mrieker/pdp8v/maindec/docs/d0ab.tif

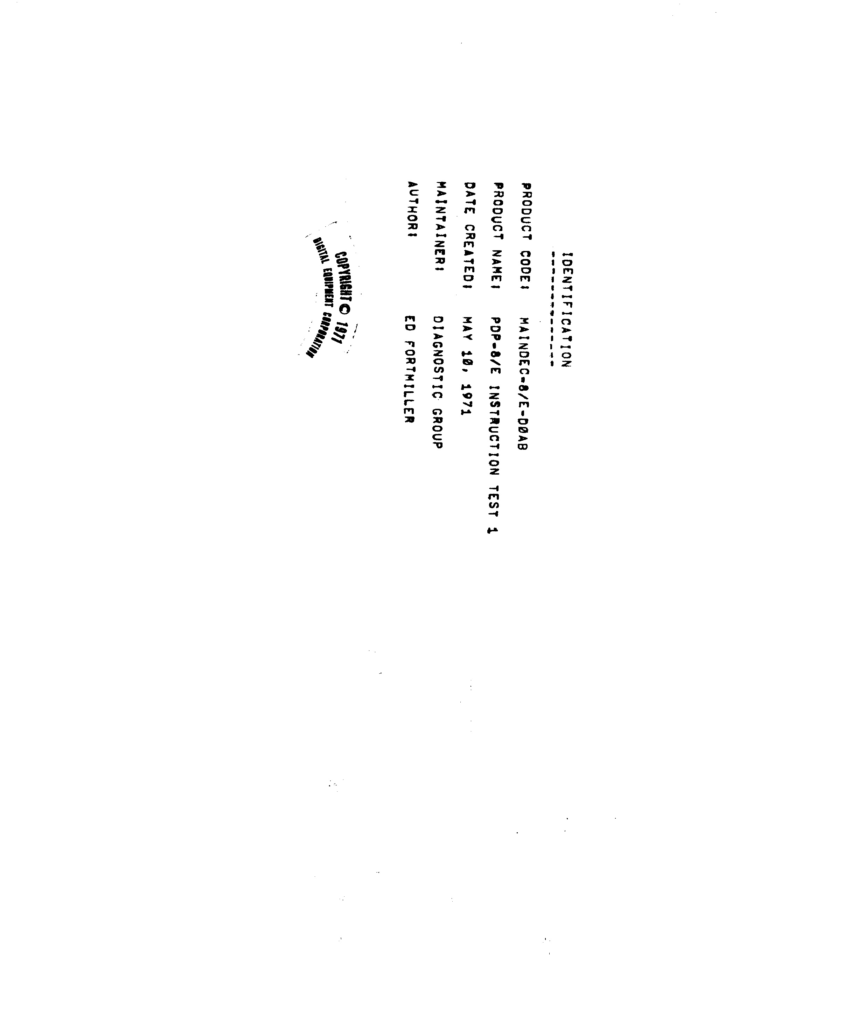
maindec/docs/d0ab.tif
