mrieker/pdp8v/maindec/docs/d0db-d.tif

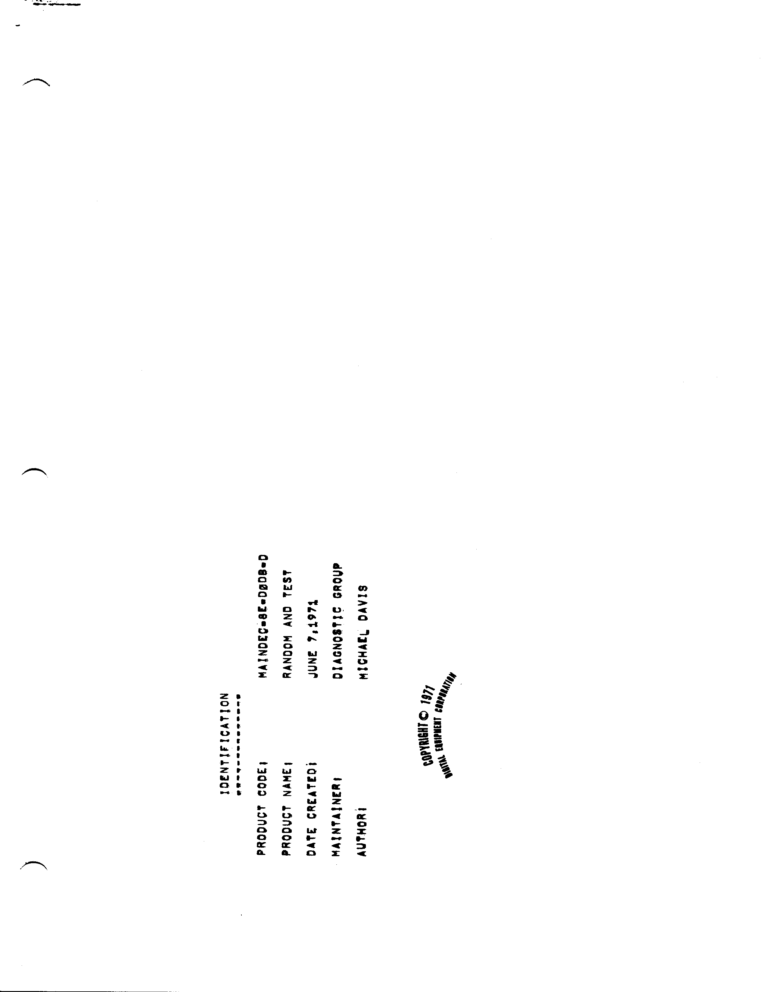
maindec/docs/d0db-d.tif
