mrieker/pdp8v/kicads/eight/single-ltspice.asc

C1: cap; 0.1µ
C2: cap; 0.1µ
C3: cap; 0.1µ
D1: zener; 3.0V
R1: res; 26.7K
R2: res; 26.7K
R3: res; 46.4K
R4: res; 150K
R5: res; 220
U1: triode; 1/2-6J6
V1: voltage; 120
V2: voltage; 96
V3: voltage; 5
Named nets: 0, OUTPUT, INPUT
1: > 4V
0: < 0V
1: > 3V
0: < 0.5V
