mrieker/pdp8v/driver/pidp.cc

//    Copyright (C) Mike Rieker, Beverly, MA USA
//    www.outerworldapps.com
//
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
//    EXPECT it to FAIL when someone's HeALTh or PROpeRTy is at RISk.
//
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
//    http://www.gnu.org/licenses/gpl-2.0.html

// operate pidp panel via gpio connector
// assumes raspberry pi gpio connector is plugged into pidp panel

#include <arpa/inet.h>
#include <errno.h>
#include <fcntl.h>
#include <netdb.h>
#include <poll.h>
#include <pthread.h>
#include <stdlib.h>
#include <string.h>
#include <time.h>
#include <unistd.h>

#include "controls.h"
#include "extarith.h"
#include "gpiolib.h"
#include "memext.h"
#include "memory.h"
#include "pidp.h"
#include "rdcyc.h"
#include "shadow.h"

// gpio pins

                    //  LR1 LR2 LR3 LR4 LR5 LR6 LR7 LR8 SR1 SR2 SR3
#define COL1    14  //  pc1 ma1 mb1 ac1 mq1 and cad df1 sw1 df1 start   [MSB]
#define COL2    15  //  pc2 ma2 mb2 ac2 mq2 tad brk df2 sw2 df2 ldaddr
#define COL3     4  //  pc3 ma3 mb3 ac3 mq3 isz ion df3 sw3 df3 dep
#define COL4     5  //   .   .   .   .   .  dca pau if1  .  if1 exam
#define COL5     6  //   .   .   .   .   .  jms run if2  .  if2 cont
#define COL6     7  //   .   .   .   .   .  jmp sc1 if3  .  if3 stop
#define COL7     8  //   .   .   .   .   .  iot sc2 lnk  .      sstep
#define COL8     9  //   .   .   .   .   .  opr sc3      .      sinst
#define COL9    10  //   .   .   .   .   .  fet sc4      .
#define COL10   11  //   .   .   .   .   .  exe sc5      .
#define COL11   12  //   .   .   .   .   .  def          .
#define COL12   13  //   .   .   .   .   .  wct          .              [LSB]

#define COLMIN 4
#define COLMASK 0xFFF0

static bool inlimbo;
static bool lastdepos;
static bool running;
static pthread_t threadid;
static uint16_t dfifswitches;
static uint16_t ledscrams[4096];
static uint16_t swunscrams[65536>>COLMIN];

static void *pidpthread (void *dummy);
static void startbutton (uint32_t buttons);
static void ldaddrbutton ();
static void deposbutton ();
static void exambutton ();
static void contbutton (uint32_t buttons);
static void stopbutton ();
static void loadpcma (uint16_t newpc, uint16_t newma);
static bool atendofmajorstate ();

void pidp_start ()
{
    ASSERT (threadid == 0);
    running = true;
    int rc = createthread (&threadid, pidpthread, NULL);
    if (rc != 0) ABORT ();
}

void pidp_stop ()
{
    running = false;
    if (threadid != 0) {
        pthread_join (threadid, NULL);
        threadid = 0;
    }
}

static void *pidpthread (void *dummy)
{
    uint32_t buttonring[8];
    uint32_t lastbuttons = 0;
    uint32_t opcodeleds[8];
    uint32_t stateleds[16];
    int buttonindex = 0;

    memset (buttonring, 0, sizeof buttonring);
    memset (opcodeleds, 0, sizeof opcodeleds);
    memset (stateleds, 0, sizeof stateleds);

    opcodeleds[0] = 1 << COL1;
    opcodeleds[1] = 1 << COL2;
    opcodeleds[2] = 1 << COL3;
    opcodeleds[3] = 1 << COL4;
    opcodeleds[4] = 1 << COL5;
    opcodeleds[5] = 1 << COL6;
    opcodeleds[6] = 1 << COL7;
    opcodeleds[7] = 1 << COL8;

    stateleds[(int)Shadow::State::FETCH1] = 1 << COL9;
    stateleds[(int)Shadow::State::FETCH2] = 1 << COL9;
    stateleds[(int)Shadow::State::DEFER1] = 1 << COL11;
    stateleds[(int)Shadow::State::DEFER2] = 1 << COL11;
    stateleds[(int)Shadow::State::DEFER3] = 1 << COL11;
    stateleds[(int)Shadow::State::EXEC1]  = 1 << COL10;
    stateleds[(int)Shadow::State::EXEC2]  = 1 << COL10;
    stateleds[(int)Shadow::State::EXEC3]  = 1 << COL10;

    for (uint16_t data = 0; data <= 07777; data ++) {
        uint16_t gpio = 0;
        if (data & 04000) gpio |= 1 << COL1;
        if (data & 02000) gpio |= 1 << COL2;
        if (data & 01000) gpio |= 1 << COL3;
        if (data & 00400) gpio |= 1 << COL4;
        if (data & 00200) gpio |= 1 << COL5;
        if (data & 00100) gpio |= 1 << COL6;
        if (data & 00040) gpio |= 1 << COL7;
        if (data & 00020) gpio |= 1 << COL8;
        if (data & 00010) gpio |= 1 << COL9;
        if (data & 00004) gpio |= 1 << COL10;
        if (data & 00002) gpio |= 1 << COL11;
        if (data & 00001) gpio |= 1 << COL12;
        ledscrams[data] = gpio;
    }

    for (uint32_t gpio = 0; gpio <= 0xFFFFU; gpio += 1 << COLMIN) {
        uint16_t data = 0;
        if (gpio & (1 << COL1))  data |= 04000;
        if (gpio & (1 << COL2))  data |= 02000;
        if (gpio & (1 << COL3))  data |= 01000;
        if (gpio & (1 << COL4))  data |= 00400;
        if (gpio & (1 << COL5))  data |= 00200;
        if (gpio & (1 << COL6))  data |= 00100;
        if (gpio & (1 << COL7))  data |= 00040;
        if (gpio & (1 << COL8))  data |= 00020;
        if (gpio & (1 << COL9))  data |= 00010;
        if (gpio & (1 << COL10)) data |= 00004;
        if (gpio & (1 << COL11)) data |= 00002;
        if (gpio & (1 << COL12)) data |= 00001;
        swunscrams[gpio>>COLMIN] = data;
    }

    // set up sequence number gt anything previously used
    PiDPMsg pidpmsg;
    memset (&pidpmsg, 0, sizeof pidpmsg);
    struct timespec nowts;
    if (clock_gettime (CLOCK_REALTIME, &nowts) < 0) ABORT ();
    pidpmsg.seq = nowts.tv_sec * 1000000000ULL + nowts.tv_nsec;

    while (running) {
        pidpmsg.seq ++;

        uint32_t lr7 =
            (memext.intenabd ()  ? (1 << COL3) : 0) |               // ION
            (waitingforinterrupt ? (1 << COL4) : 0) |               // PAUSE (we use it for 'wait for interrupt')
            (ctl_isstopped ()    ? 0 : (1 << COL5)) |               // RUN
            ledscrams[extarith.stepcount<<2];                       // SC

        uint16_t membuffer;
        uint32_t lr6 = 0;
        if (inlimbo) {

            // ldaddr/exam/depos, show mem contents
            membuffer = memarray[memext.iframe|shadow.r.ma];
        } else {

            // not doing ldaddr/exam/depos, show processor state
            Shadow::State st = (Shadow::State) (shadow.r.state & 15);
            lr6 = stateleds[(int)st];
            if ((st != Shadow::State::FETCH1) && (st != Shadow::State::INTAK1)) {
                uint32_t ir = (st == Shadow::State::FETCH2) ? (gpio->readgpio () & G_DATA) / G_DATA0 : shadow.r.ir;
                lr6 |= opcodeleds[(ir>>9)&7];
            }

            if (st == Shadow::State::INTAK1) lr7 |= 1 << COL2;      // BREAK (we use it for INTAK1 cycle)

            membuffer = (gpio->readgpio () & G_DATA) / G_DATA0;     // show what is on gpio bus
        }

        uint32_t lr8 =
            ledscrams[(memext.dframe>>3)|(memext.iframe>>6)] |
            (shadow.r.link ? (1 << COL7) : 0);

        // output LED rows
        pidpmsg.ledrows[0] = ledscrams[shadow.r.pc];
        pidpmsg.ledrows[1] = ledscrams[shadow.r.ma];
        pidpmsg.ledrows[2] = ledscrams[membuffer];
        pidpmsg.ledrows[3] = ledscrams[shadow.r.ac];
        pidpmsg.ledrows[4] = ledscrams[extarith.multquot];
        pidpmsg.ledrows[5] = lr6;
        pidpmsg.ledrows[6] = lr7;
        pidpmsg.ledrows[7] = lr8;

        // ... also read switches
        if (! pidp_proc (&pidpmsg)) continue;

        // row 1 - switch register switches
        switchregister = swunscrams[(~pidpmsg.swrows[0]&COLMASK)>>COLMIN];

        // row 2 - data field, instr field switches
        dfifswitches   = swunscrams[(~pidpmsg.swrows[1]&COLMASK)>>COLMIN];

        // row 3 - control buttons
        uint32_t buttons = ~ pidpmsg.swrows[2] & COLMASK;
        buttonring[buttonindex] = buttons;
        buttonindex = (buttonindex + 1) % 8;

        // if button went from not pressed to pressed, perform function
        uint32_t butpressed = ~ lastbuttons & buttons;

        // if buttons have been steady past 8 iterations, we consider the buttons valid
        for (int i = 0; ++ i < 8;) {
            if (buttonring[i] != buttons) goto badbuttons;
        }

        if (butpressed & (1 << COL1)) startbutton (buttons);
        if (butpressed & (1 << COL2)) ldaddrbutton ();
        if (butpressed & (1 << COL3)) deposbutton ();
        if (butpressed & (1 << COL4)) exambutton ();
        if (butpressed & (1 << COL5)) contbutton (buttons);
        if (butpressed & (1 << COL6)) stopbutton ();
        lastbuttons = buttons;
    badbuttons:;
    }

    return NULL;
}

// reset I/O then start at address in IF/PC
static void startbutton (uint32_t buttons)
{
    if (ctl_isstopped ()) {
        ctl_reset (memext.iframe | shadow.r.pc, true);
        contbutton (buttons);
    }
}

// load switch register into MA and PC, then show contents of that location
static void ldaddrbutton ()
{
    if (ctl_isstopped ()) {
        loadpcma (switchregister, switchregister);
        memext.dframe = (dfifswitches & 07000) << 3;
        memext.iframe = (dfifswitches & 00700) << 6;
        inlimbo   = true;
        lastdepos = false;
    }
}

// if last button was deposit, increment MA
// then in any case, deposit switch register into MA location
static void deposbutton ()
{
    if (ctl_isstopped ()) {
        uint16_t ma = shadow.r.ma;
        if (lastdepos) {
            ma = (ma + 1) & 07777;
            loadpcma (shadow.r.pc, ma);
        }
        memarray[memext.iframe|ma] = switchregister;
        inlimbo   = true;
        lastdepos = true;
    }
}

// if last button wasn't deposit, increment MA
// then in any case, show memory contents
static void exambutton ()
{
    if (ctl_isstopped ()) {
        uint16_t ma = shadow.r.ma;
        if (! lastdepos) {
            ma = (ma + 1) & 07777;
            loadpcma (shadow.r.pc, ma);
        }
        inlimbo   = true;
        lastdepos = false;
    }
}

// resume execution at program counter location, subject to step switches
static void contbutton (uint32_t buttons)
{
    if (ctl_isstopped ()) {
        if (buttons & (1 << COL7)) {
            do ctl_stepcyc ();  // single step - step one major state
            while (! atendofmajorstate ());
        } else if (buttons & (1 << COL8)) {
            ctl_stepins ();     // single instr - step one instruction
                                // stops in middle of FETCH2 or middle of INTAK1
        } else {
            ctl_run ();         // neither - continuous run
        }
        inlimbo   = false;
        lastdepos = false;
    }
}

// stop executing instructions
static void stopbutton ()
{
    if (! ctl_isstopped ()) {
        ctl_stop ();            // stops in middle of any cycle
        while (! atendofmajorstate ()) {
            ctl_stepcyc ();     // cycle to end of major state
        }
        inlimbo   = false;
        lastdepos = false;
    }
}

// load tubes' program counter and memory address register with given values
// returns with tubes in middle of FETCH2 with clock still high
static void loadpcma (uint16_t newpc, uint16_t newma)
{
    uint16_t saveac = shadow.r.ac;
    bool savelink = shadow.r.link;
    if (! ctl_ldregs (savelink, saveac, newma, newpc)) ABORT ();
}

// stopped in middle of some cycle - see if it is the last cycle of a major state
static bool atendofmajorstate ()
{
    Shadow::State st = shadow.r.state;
    switch (st) {
        case Shadow::State::FETCH1: return false;
        case Shadow::State::FETCH2: return true;
        case Shadow::State::DEFER1: return false;
        case Shadow::State::DEFER2: return (shadow.r.ma & 07770) != 00010;
        case Shadow::State::DEFER3: return true;
        case Shadow::State::ARITH1: return false;
        case Shadow::State::AND2  : return true;
        case Shadow::State::TAD2  : return false;
        case Shadow::State::TAD3  : return true;
        case Shadow::State::ISZ1  : return false;
        case Shadow::State::ISZ2  : return false;
        case Shadow::State::ISZ3  : return true;
        case Shadow::State::DCA1  : return false;
        case Shadow::State::DCA2  : return true;
        case Shadow::State::JMP1  : return true;
        case Shadow::State::JMS1  : return false;
        case Shadow::State::JMS2  : return false;
        case Shadow::State::JMS3  : return true;
        case Shadow::State::IOT1  : return false;
        case Shadow::State::IOT2  : return true;
        case Shadow::State::GRPA1 : return true;
        case Shadow::State::GRPB1 : return true;
        case Shadow::State::INTAK1: return true;
        default: ABORT ();
    }
}
