mrieker/pdp8v/zynq/ledpins.xdc

set_property PACKAGE_PIN Y16 [get_ports LEDoutG_0]
set_property PACKAGE_PIN Y17 [get_ports LEDoutB_0]
set_property PACKAGE_PIN R14 [get_ports LEDoutR_0]
set_property IOSTANDARD LVCMOS33 [get_ports LEDoutB_0]
set_property IOSTANDARD LVCMOS33 [get_ports LEDoutG_0]
set_property IOSTANDARD LVCMOS33 [get_ports LEDoutR_0]

set_property PACKAGE_PIN G15 [get_ports EXTSDA_0]   ;# CN2-69
set_property PACKAGE_PIN H20 [get_ports EXTSCL_0]   ;# CN2-65
set_property IOSTANDARD LVCMOS33 [get_ports EXTSDA_0]
set_property IOSTANDARD LVCMOS33 [get_ports EXTSCL_0]
