mrieker/pdp8v/driver/GUIRasPiCtl.cc

//    Copyright (C) Mike Rieker, Beverly, MA USA
//    www.outerworldapps.com
//
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
//    EXPECT it to FAIL when someone's HeALTh or PROpeRTy is at RISk.
//
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
//    http://www.gnu.org/licenses/gpl-2.0.html

// inteface GUI java program to raspictl

#include "GUIRasPiCtl.h"

#include <alloca.h>
#include <pthread.h>
#include <string.h>

#include "controls.h"
#include "disassemble.h"
#include "gpiolib.h"
#include "iodevs.h"
#include "memext.h"
#include "memory.h"
#include "miscdefs.h"
#include "shadow.h"

#define EXCKR(x) x; if (env->ExceptionCheck ()) return 0

extern GpioLib *gpio;

int main (int argc, char **argv);

JNIEXPORT jint JNICALL Java_GUIRasPiCtl_main (JNIEnv *env, jclass klass, jobjectArray args)
{
    // see how many strings passed in args
    int argc = EXCKR (env->GetArrayLength (args));

    // allocate an array of pointers (one extra for NULL terminator)
    char **argv = (char **) alloca ((argc + 1) * sizeof *argv);

    // copy strings into array
    for (int i = 0; i < argc; i ++) {

        // get string from arg array element
        jstring argstr = (jstring) EXCKR (env->GetObjectArrayElement (args, i));

        // convert to UTF-8 byte array
        char const *argutf = EXCKR (env->GetStringUTFChars (argstr, NULL));

        // copy to stack
        int arglen = strlen (argutf);
        char *arg = (char *) alloca (arglen + 1);
        memcpy (arg, argutf, arglen);
        arg[arglen] = 0;
        argv[i] = arg;

        // release java string
        env->ReleaseStringUTFChars (argstr, argutf);
    }

    // NULL terminate argument list and call main
    argv[argc] = NULL;
    return main (argc, argv);
}

JNIEXPORT jint JNICALL Java_GUIRasPiCtl_getacl (JNIEnv *env, jclass klass)
{
    return (shadow.r.link ? 010000 : 0) | shadow.r.ac;
}

JNIEXPORT jint JNICALL Java_GUIRasPiCtl_getma (JNIEnv *env, jclass klass)
{
    return shadow.r.ma | memext.dframe;
}

JNIEXPORT jint JNICALL Java_GUIRasPiCtl_getpc (JNIEnv *env, jclass klass)
{
    return shadow.r.pc | memext.iframe;
}

JNIEXPORT jint JNICALL Java_GUIRasPiCtl_getir (JNIEnv *env, jclass klass)
{
    return shadow.r.ir;
}

JNIEXPORT jint JNICALL Java_GUIRasPiCtl_getst (JNIEnv *env, jclass klass)
{
    return (jint) shadow.r.state;
}

JNIEXPORT jint JNICALL Java_GUIRasPiCtl_getgpio (JNIEnv *env, jclass klass)
{
    GpioLib *g = gpio;
    if (g == NULL) return -1;
    return g->readgpio ();
}

JNIEXPORT jlong JNICALL Java_GUIRasPiCtl_getcycs (JNIEnv *env, jclass klass)
{
    return shadow.getcycles ();
}

JNIEXPORT jint JNICALL Java_GUIRasPiCtl_getsr (JNIEnv *env, jclass klass)
{
    return switchregister;
}

JNIEXPORT void JNICALL Java_GUIRasPiCtl_setsr (JNIEnv *env, jclass klass, jint sr)
{
    switchregister = sr & 32767;
}

// returns true = processor is stopped
//        false = processor is running
JNIEXPORT jboolean JNICALL Java_GUIRasPiCtl_getstop (JNIEnv *env, jclass klass)
{
    return ctl_isstopped ();
}

// input:
//  stop = true: stop the processor
//        false: run the processor
// returns:
//    true = was stopped
//   false = was running
JNIEXPORT jboolean JNICALL Java_GUIRasPiCtl_setstop (JNIEnv *env, jclass klass, jboolean stop)
{
    return stop ? ctl_stop () : ctl_run ();
}

// returns:
//   true = was stopped, stepped one cycle, now stopped again
//  false = was running, not stepped, still running
JNIEXPORT jboolean JNICALL Java_GUIRasPiCtl_stepcyc (JNIEnv *env, jclass klass)
{
    return ctl_stepcyc ();
}

// returns:
//   true = was stopped, stepped to FETCH2 or INTAK1, now stopped again
//  false = was running, not stepped, still running
JNIEXPORT jboolean JNICALL Java_GUIRasPiCtl_stepins (JNIEnv *env, jclass klass)
{
    return ctl_stepins ();
}

JNIEXPORT jstring JNICALL Java_GUIRasPiCtl_disassemble (JNIEnv *env, jclass klass, jint ir, jint pc)
{
    char const *io = iodisas (ir);
    if (io != NULL) return env->NewStringUTF (io);
    std::string str = disassemble (ir, pc);
    return env->NewStringUTF (str.c_str ());
}

JNIEXPORT jint JNICALL Java_GUIRasPiCtl_rdmem (JNIEnv *env, jclass klass, jint addr)
{
    if (addr >= MEMSIZE) return -1;
    return memarray[addr];
}

JNIEXPORT jint JNICALL Java_GUIRasPiCtl_wrmem (JNIEnv *env, jclass klass, jint addr, jint data)
{
    if (addr >= MEMSIZE) return -1;
    data &= 07777;
    memarray[addr] = data;
    return data;
}

// returns:
//   true = was stopped, reset, now stopped again at end of FETCH1
//  false = failed
JNIEXPORT jboolean JNICALL Java_GUIRasPiCtl_reset (JNIEnv *env, jclass klass, jint addr, jboolean resio)
{
    return ctl_reset (addr, resio);
}

// load registers
// returns:
//   true = was stopped, reset, now stopped again at end of FETCH1
//  false = failed
JNIEXPORT jboolean JNICALL Java_GUIRasPiCtl_ldregs (JNIEnv *env, jclass klass, jboolean link, jint ac, jint ma, jint pc)
{
    return ctl_ldregs (link, ac, ma, pc);
}
