mrieker/pdp8v/driver/exptimingioin.cc

// runs on raspi plugged into experiment board (exp)
// measures clock frequency of IOS,MQL->IOIN gate

// ./loadmod.sh
// ./exptimingioin.armv6l

#include <stdio.h>
#include <string.h>
#include <time.h>
#include <unistd.h>

#include "gpiolib.h"
#include "rdcyc.h"

static GpioLib *gpiolib;
static uint32_t fullus;

static void waitfull ();

int main ()
{
    struct timespec finished, started;

    setlinebuf (stdout);

    gpiolib = new PhysLib (10, true);
    gpiolib->open ();
    gpiolib->writegpio (false, G_RESET);
    gpiolib->halfcycle ();
    gpiolib->halfcycle ();
    gpiolib->halfcycle ();
    gpiolib->writegpio (false, 0);

    for (fullus = 1; fullus <= 20; fullus ++) {
        int bad = 0;
        if (clock_gettime (CLOCK_REALTIME, &started) < 0) ABORT ();
        for (int i = 0; i < 10000; i ++) {
            uint32_t gray = (i & 3) ^ ((i & 3) >> 1);
            uint32_t sent = ((gray & 1) ? G_LINK : 0) | ((gray & 2) ? G_IOS : 0);
            gpiolib->writegpio (true, sent);
            waitfull ();
            uint32_t rcvd = gpiolib->readgpio () & G_IOIN;
            bad += (((sent / G_LINK) ^ (sent / G_IOS)) & 1) ^ (rcvd / G_IOIN);
        }
        if (clock_gettime (CLOCK_REALTIME, &finished) < 0) ABORT ();
        uint64_t elapsedns = (uint64_t) (finished.tv_sec - started.tv_sec) * 1000000000 + finished.tv_nsec - started.tv_nsec;
        printf (" fullus = %2u  bad = %5u/10000  %6llu Hz\n", fullus, bad, 10000000000000ULL / elapsedns);
    }
    return 0;
}

static void waitfull ()
{
    uint32_t start = rdcyc ();
    while (rdcyc () - start < fullus) { }
}
