mrieker/pdp8v/driver/iodevtc08.cc

//    Copyright (C) Mike Rieker, Beverly, MA USA
//    www.outerworldapps.com
//
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
//    EXPECT it to FAIL when someone's HeALTh or PROpeRTy is at RISk.
//
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
//    http://www.gnu.org/licenses/gpl-2.0.html

// TC08 controller maintenance 1970
// boot code: OS/8 Handbook April 1974, p41
//  07613: 06774, 01222, 06766, 06771, 05216, 01223, 05215, 00600, 00220

// files are 1474*129*2 bytes = 380292 bytes
// loading a file read/write extends/truncates it to correct size
// if read/write file was null length, it is formatted for OS/8

#include <errno.h>
#include <fcntl.h>
#include <signal.h>
#include <stdarg.h>
#include <stdio.h>
#include <string.h>
#include <sys/file.h>
#include <sys/mman.h>
#include <sys/time.h>
#include <unistd.h>

#include "dyndis.h"
#include "gpiolib.h"
#include "iodevtc08.h"
#include "memext.h"
#include "memory.h"
#include "rdcyc.h"
#include "shadow.h"

/*
  status_a:
    | unitsel   |REV|GO |CON|  opcode   |IEN|PAF|PSF|
    +---+---+---+---+---+---+---+---+---+---+---+---+
    | 4   2   1 | 4   2   1 | 4   2   1 | 4   2   1 |

  status_b:
    |ERR|   |EOT|SEL|       | dma field |       |SUC|
    +---+---+---+---+---+---+---+---+---+---+---+---+
    | 4   2   1 | 4   2   1 | 4   2   1 | 4   2   1 |
*/

#define DBGPR if (shm->debug > 0) dbgpr

#define MIN(a,b) (((a) < (b)) ? (a) : (b))

#define BLOCKSPERTAPE 1474  // 02702
#define WORDSPERBLOCK 129
#define BYTESPERBLOCK (WORDSPERBLOCK*2)
#define UNLOADNS 5000000000ULL

#define CONTIN (shm->status_a & 00100)
#define NORMAL (! CONTIN)

#define REVBIT 00400
#define GOBIT  00200

#define REVERS (shm->status_a & REVBIT)
#define FORWRD (! REVERS)

#define DTFLAG 00001    // successful completion
#define ERFLAG 04000    // error completion
#define ERRORS 07700
#define ENDTAP 05000
#define SELERR 04400

#define INTENA 00004    // interrupt enable
#define INTREQ 04001    // request interrupt if error or success

#define IDWC 07754      // memory word containing 2s comp dma word count
#define IDCA 07755      // memory word containing dma address minus one

IODevTC08 iodevtc08;

static uint16_t ocarray[4096];

static IODevOps const iodevops[] = {
    { 06761, "DTRA (TC08) read status register A" },
    { 06762, "DTCA (TC08) clear status register A" },
    { 06764, "DTXA (TC08) load status register A" },
    { 06766, "DTLA (TC08) clear and load status register A" },
    { 06771, "DTSF (TC08) skip on flag" },
    { 06772, "DTRB (TC08) read status register B" },
    { 06773, "DTSF DTRB (TC08) skip on flag, read status register B" },
    { 06774, "DTXB (TC08) load status register B and clear accumulator" },
};

static char const *const cmdmnes[8] = { "MOVE", "SRCH", "RDAT", "RALL", "WDAT", "WALL", "WTIM", "ERR7" };

static uint64_t getnowns ();
static bool dmareadoverwritesinstructions (uint16_t field, uint16_t idca, uint16_t idwc);
static SCRetErr *writeformat (int fd);

IODevTC08::IODevTC08 ()
{
    opscount = sizeof iodevops / sizeof iodevops[0];
    opsarray = iodevops;

    iodevname = "tc08";

    // initialize obverse complement lookup table
    //   abcdefghijkl <=> ~jklghidefabc
    for (int i = 0; i < 4096; i ++) {
        uint16_t reverse = 07777;
        for (int j = 0; j < 12; j += 3) {
            uint32_t threebits = (i >> j) & 7;
            reverse -= threebits << (9 - j);
        }
        ocarray[i] = reverse;
    }

    // initialize everything
    this->shm = NULL;
    this->shmfd = -1;
    this->allowskipopt = true;
    this->dskpwait = false;
}

IODevTC08::~IODevTC08 ()
{
    // nothing to do if shared memory was never set up
    if (this->shm == NULL) return;

    // lock and unlock for a barrier
    pthread_mutex_lock (&shm->lock);
    shm->exiting = true;
    pthread_mutex_unlock (&shm->lock);

    // stop thread
    this->ioreset ();

    // delete shared memory
    shm_unlink (shmname);
    for (int i = 0; i < 8; i ++) {
        close (shm->drives[i].dtfd);
        shm->drives[i].dtfd = -1;
        shm->drives[i].fname[0] = 0;
    }
    munmap (this->shm, sizeof *this->shm);
    this->shm = NULL;
    close (this->shmfd);
    this->shmfd = -1;
}

// reset the device
// - kill thread
void IODevTC08::ioreset ()
{
    // nothing to do if shared memory isn't set up
    if (this->shm == NULL) return;

    pthread_mutex_lock (&shm->lock);

    // if another thread is doing the reset, wait for it to complete
    if (shm->resetting) {
        do pthread_cond_wait (&shm->cond, &shm->lock);
        while (shm->resetting);
    } else {

        // no other thread doing reset, tell others we are doing reset
        shm->resetting = true;
        pthread_cond_broadcast (&shm->cond);

        // if our thread is running, tell it to stop and wait for it to stop
        if (shm->threadid != 0) {
            pthread_mutex_unlock (&shm->lock);
            pthread_join (shm->threadid, NULL);
            pthread_mutex_lock (&shm->lock);
            shm->threadid = 0;
        }

        // clear status to reset state
        shm->status_a = 0;
        shm->status_b = 0;
        clrintreqmask (IRQ_DTAPE);

        shm->resetting = false;
        pthread_cond_broadcast (&shm->cond);
    }

    pthread_mutex_unlock (&shm->lock);
}

// load/unload files
SCRet *IODevTC08::scriptcmd (int argc, char const *const *argv)
{
    // create shared memory if not already
    if (this->shm == NULL) {

        // create shared memory for tc08status.cc program to access tape state
        this->shmfd = shm_open (shmname, O_RDWR | O_CREAT, 0600);
        if (this->shmfd < 0) {
            fprintf (stderr, "IODevTC08::IODevTC08: error creating shared memory %s: %m\n", shmname);
            ABORT ();
        }
        if (ftruncate (this->shmfd, sizeof *this->shm) < 0) {
            fprintf (stderr, "IODevTC08::IODevTC08: error setting shared memory %s size: %m\n", shmname);
            close (this->shmfd);
            this->shmfd = -1;
            shm_unlink (shmname);
            ABORT ();
        }

        // map it to va space and zero it out
        void *shmptr = mmap (NULL, sizeof *this->shm, PROT_READ | PROT_WRITE, MAP_SHARED, this->shmfd, 0);
        if (shmptr == MAP_FAILED) {
            fprintf (stderr, "IODevTC08::IODevTC08: error accessing shared memory %s: %m\n", shmname);
            close (this->shmfd);
            this->shmfd = -1;
            shm_unlink (shmname);
            ABORT ();
        }

        IODevTC08Shm *lclshm = (IODevTC08Shm *) shmptr;
        memset (lclshm, 0, sizeof *lclshm);

        // initialize everything
        pthread_condattr_t condattrs;
        if (pthread_condattr_init (&condattrs) != 0) ABORT ();
        if (pthread_condattr_setpshared (&condattrs, PTHREAD_PROCESS_SHARED) != 0) ABORT ();
        if (pthread_cond_init (&lclshm->cond, &condattrs) != 0) ABORT ();

        pthread_mutexattr_t lockattrs;
        if (pthread_mutexattr_init (&lockattrs) != 0) ABORT ();
        if (pthread_mutexattr_setpshared (&lockattrs, PTHREAD_PROCESS_SHARED) != 0) ABORT ();
        if (pthread_mutex_init (&lclshm->lock, &lockattrs) != 0) ABORT ();

        lclshm->dtpid = getpid ();
        for (int i = 0; i < 8; i ++) {
            lclshm->drives[i].dtfd = -1;
            lclshm->drives[i].unldat = 0xFFFFFFFFFFFFFFFFULL;
        }

        // lock and unlock for a barrier
        pthread_mutex_lock (&lclshm->lock);
        lclshm->initted = true;
        pthread_mutex_unlock (&lclshm->lock);
        this->shm = lclshm;
    }

    // debug <level>
    if (strcmp (argv[0], "debug") == 0) {
        if (argc == 1) {
            return new SCRetInt (shm->debug);
        }

        if (argc == 2) {
            shm->debug = atoi (argv[1]);
            return NULL;
        }

        return new SCRetErr ("iodev %s debug <level>", iodevname);
    }

    if (strcmp (argv[0], "help") == 0) {
        puts ("");
        puts ("valid sub-commands:");
        puts ("");
        puts ("  debug                           - get debug level");
        puts ("  debug <level>                   - set debug level");
        puts ("  loaded <drivenumber>            - see what file is loaded on drive");
        puts ("                                    first char -: read-only; +: read/write");
        puts ("  loadro <drivenumber> <filename> - load file write-locked");
        puts ("  loadrw <drivenumber> <filename> - load file write-enabled");
        puts ("  unload <drivenumber>            - unload file - drive reports offline");
        puts ("");
        return NULL;
    }

    // return name of file loaded on drive (null if none)
    if (strcmp (argv[0], "loaded") == 0) {
        if (argc == 2) {
            char *p;
            int driveno = strtol (argv[1], &p, 0);
            if ((*p != 0) || (driveno < 0) || (driveno > 7)) return new SCRetErr ("drivenumber %s not in range 0..7", argv[1]);
            IODevTC08Drive *drive = &shm->drives[driveno];
            if (drive->dtfd < 0) return NULL;
            return new SCRetStr ("%c%s", drive->rdonly ? '-' : '+', drive->fname);
        }

        return new SCRetErr ("iodev tc08 loaded <drivenumber>");
    }

    // loadro/loadrw <drivenumber> <filename>
    bool loadro = (strcmp (argv[0], "loadro") == 0);
    bool loadrw = (strcmp (argv[0], "loadrw") == 0);
    if (loadro | loadrw) {
        if (argc == 3) {
            char *p;
            int driveno = strtol (argv[1], &p, 0);
            if ((*p != 0) || (driveno < 0) || (driveno > 7)) return new SCRetErr ("drivenumber %s not in range 0..7", argv[1]);
            int fd = open (argv[2], loadrw ? O_RDWR | O_CREAT : O_RDONLY, 0666);
            if (fd < 0) return new SCRetErr (strerror (errno));
            char *lockerr = lockfile (fd, loadro ? F_RDLCK : F_WRLCK);
            if (lockerr != NULL) {
                SCRetErr *err = new SCRetErr ("%s", lockerr);
                close (fd);
                free (lockerr);
                return err;
            }
            long oldsize = lseek (fd, 0, SEEK_END);
            if (loadrw && (ftruncate (fd, BYTESPERBLOCK * BLOCKSPERTAPE) < 0)) {
                SCRetErr *err = new SCRetErr ("%m");
                close (fd);
                return err;
            }
            if (loadrw && (oldsize == 0)) {
                SCRetErr *err = writeformat (fd);
                if (err != NULL) {
                    close (fd);
                    return err;
                }
            }
            fprintf (stderr, "IODevTC08::scriptcmd: drive %d loaded with read%s file %s\n", driveno, (loadro ? "-only" : "/write"), argv[2]);
            pthread_mutex_lock (&shm->lock);
            IODevTC08Drive *drive = &shm->drives[driveno];
            close (drive->dtfd);
            drive->dtfd    = fd;
            drive->rdonly  = loadro;
            drive->tapepos = 0;
            drive->unldat  = 0xFFFFFFFFFFFFFFFFULL;
            strncpy (drive->fname, argv[2], sizeof drive->fname);
            drive->fname[sizeof drive->fname-1] = 0;
            pthread_mutex_unlock (&shm->lock);
            return NULL;
        }

        return new SCRetErr ("iodev tc08 loadro/loadrw <drivenumber> <filename>");
    }

    // unload <drivenumber>
    if (strcmp (argv[0], "unload") == 0) {
        if (argc == 2) {
            char *p;
            int driveno = strtol (argv[1], &p, 0);
            if ((*p != 0) || (driveno < 0) || (driveno > 7)) return new SCRetErr ("drivenumber %s not in range 0..7", argv[1]);
            pthread_mutex_lock (&shm->lock);
            this->unloadrive (driveno);
            pthread_mutex_unlock (&shm->lock);
            return NULL;
        }

        return new SCRetErr ("iodev tc08 unload <drivenumber>");
    }

    return new SCRetErr ("unknown tape command %s - valid: help loaded loadro loadrw unload", argv[0]);
}

// perform i/o instruction
uint16_t IODevTC08::ioinstr (uint16_t opcode, uint16_t input)
{
    return (this->shm == NULL) ? ioinstroffline (opcode, input) : ioinstronline (opcode, input);
}

// - no shared memory, report drive offline status
uint16_t IODevTC08::ioinstroffline (uint16_t opcode, uint16_t input)
{
    switch (opcode) {

        // DTRA (TC08) read status register A
        // p 396
        case 06761: {
            break;
        }

        // DTCA (TC08) clear status register A
        case 06762: {
            break;
        }

        // DTLA (TC08) clear and load status register A
        case 06766: {
            // fall through
        }

        // DTXA (TC08) load status register A
        case 06764: {
            input &= IO_LINK;
            break;
        }

        // DTSF (TC08) skip on flag
        case 06771: {
            input |= IO_SKIP;
            break;
        }

        // DTRB (TC08) read status register B
        case 06772: {
            input |= SELERR;
            break;
        }

        // DTSF (TC08) skip on flag
        // DTRB (TC08) read status register B
        case 06773: {
            input |= IO_SKIP | SELERR;
            break;
        }

        // DTXB (TC08) load status register B <05:03> and clear accumulator
        case 06774: {
            input &= IO_LINK;
            break;
        }

        default: {
            input = UNSUPIO;
            break;
        }
    }
    return input;
}

// - have shared memory, process i/o instruction
uint16_t IODevTC08::ioinstronline (uint16_t opcode, uint16_t input)
{
    pthread_mutex_lock (&shm->lock);

    uint16_t oldstata = shm->status_a;

    DBGPR (2, "IODevTC08::ioinstr: %05o %s\n", lastreadaddr, iodisas (opcode));

    switch (opcode) {

        // DTRA (TC08) read status register A
        // p 396
        case 06761: {
            DBGPR (2, "IODevTC08::ioinstr: read status_a %04o\n", shm->status_a);
            input |= shm->status_a;
            break;
        }

        // DTCA (TC08) clear status register A
        case 06762: {
            DBGPR (2, "IODevTC08::ioinstr: clear status_a\n");
            shm->status_a = 0;
            updateirq ();
            break;
        }

        // DTLA (TC08) clear and load status register A
        case 06766: {
            DBGPR (2, "IODevTC08::ioinstr: clear status_a\n");
            shm->status_a = 0;
            // fall through
        }

        // DTXA (TC08) load status register A
        case 06764: {
            shm->status_a ^= input & 07774;
            DBGPR (2, "IODevTC08::ioinstr: xor status_a with %04o giving %04o\n", input & 07774, shm->status_a);
            if (! (input & 00001)) {
                DBGPR (2, "IODevTC08::ioinstr: clear dectape flag\n");
                shm->status_b &= ~ DTFLAG;  // clear dectape flag
            }
            if (! (input & 00002)) {
                DBGPR (2, "IODevTC08::ioinstr: clear error flags\n");
                shm->status_b &= ~ ERRORS;  // clear all error flags
            }
            updateirq ();

            int driveno = (shm->status_a >> 9) & 7;
            IODevTC08Drive *drive = &shm->drives[driveno];
            drive->unldat = 0xFFFFFFFFFFFFFFFFULL;
            DBGPR (1, "IODevTC08::ioinstr: st_A=%04o  st_B=%04o  startio  %o %s %s %s %s  tpos=%04o%c\n",
                    shm->status_a, shm->status_b, (shm->status_a >> 9) & 7, CONTIN ? "CON" : "NOR",
                    (shm->status_a & REVBIT) ? "REV" : "FWD", (shm->status_a & GOBIT) ? "GO" : "ST",
                    cmdmnes[(shm->status_a&070)>>3], drive->tapepos / 4, (drive->tapepos & 3) + 'a');

            if ((shm->status_a ^ oldstata) & (GOBIT | REVBIT)) {
                shm->startdelay = true;                     // additional delay if direction changed or just started or stopped
            }
            if (shm->status_a & GOBIT) {
                shm->iopend = true;                         // there is an i/o command to process
                shm->dmapc  = dyndispc;
                shm->cycles = shadow.getcycles ();
                pthread_cond_broadcast (&shm->cond);
                if (shm->threadid == 0) {
                    int rc = createthread (&shm->threadid, threadwrap, this);
                    if (rc != 0) ABORT ();
                }
            }

            input &= IO_LINK;                               // clear accumulator
            break;
        }

        // DTSF (TC08) skip on flag
        case 06771: {
            DBGPR (2, "IODevTC08::ioinstr: skip on flag %04o = %s\n", shm->status_b, ((shm->status_b & INTREQ) ? "TRUE" : "FALSE"));
            if (shm->status_b & INTREQ) input |= IO_SKIP;
            else if (this->allowskipopt) skipoptwait (opcode, &shm->lock, &this->dskpwait);
            break;
        }

        // DTRB (TC08) read status register B
        case 06772: {
            DBGPR (2, "IODevTC08::ioinstr: read status_b %04o\n", shm->status_b);
            input |= shm->status_b;
            break;
        }

        // DTSF (TC08) skip on flag
        // DTRB (TC08) read status register B
        case 06773: {
            DBGPR (2, "IODevTC08::ioinstr: read status_b %04o\n", shm->status_b);
            DBGPR (2, "IODevTC08::ioinstr: skip on flag %04o = %s\n", shm->status_b, ((shm->status_b & INTREQ) ? "TRUE" : "FALSE"));
            input |= shm->status_b;
            if (shm->status_b & INTREQ) input |= IO_SKIP;
            else if (this->allowskipopt) skipoptwait (opcode, &shm->lock, &this->dskpwait);
            break;
        }

        // DTXB (TC08) load status register B <05:03> and clear accumulator
        case 06774: {
            shm->status_b = (shm->status_b & 07707) | (input & 00070);
            DBGPR (2, "IODevTC08::ioinstr: load status_b %04o\n", shm->status_b);
            input &= IO_LINK;
            break;
        }

        default: {
            input = UNSUPIO;
            break;
        }
    }
    pthread_mutex_unlock (&shm->lock);
    return input;
}

// thread what does the tape file I/O
void *IODevTC08::threadwrap (void *zhis)
{
    ((IODevTC08 *)zhis)->thread ();
    return NULL;
}

void IODevTC08::thread ()
{
    pthread_mutex_lock (&shm->lock);
    while (! shm->resetting) {

        // waiting for another I/O request
        if (! shm->iopend) {

            // unload drives that were left running for UNLOADNS
            uint64_t nowns = getnowns ();
            uint64_t earliestunload = 0xFFFFFFFFFFFFFFFFULL;
            for (int i = 0; i < 8; i ++) {
                IODevTC08Drive *drive = &shm->drives[i];
                if (nowns > drive->unldat) this->unloadrive (i);
                if (earliestunload > drive->unldat) earliestunload = drive->unldat;
            }

            // wait for another I/O or a drive to unload
            if (earliestunload < 0xFFFFFFFFFFFFFFFFULL) {
                struct timespec unldts;
                unldts.tv_sec  = earliestunload / 1000000000;
                unldts.tv_nsec = earliestunload % 1000000000;
                int rc = pthread_cond_timedwait (&shm->cond, &shm->lock, &unldts);
                if ((rc != 0) && (rc != ETIMEDOUT)) ABORT ();
            } else {
                int rc = pthread_cond_wait (&shm->cond, &shm->lock);
                if (rc != 0) ABORT ();
            }
        } else {
            shm->iopend = false;

            uint16_t oldidwc = memarray[IDWC];
            uint16_t field = (shm->status_b & 070) << 9;

            DBGPR (1, "IODevTC08::thread: start st_A=%04o st_B=%04o idwc=%04o idca=%04o\n", shm->status_a, shm->status_b, oldidwc, memarray[IDCA]);

            int driveno = (shm->status_a >> 9) & 007;
            IODevTC08Drive *drive = &shm->drives[driveno];
            drive->unldat = 0xFFFFFFFFFFFFFFFFULL;

            // select error if no tape loaded
            if (drive->dtfd < 0) {
                shm->status_b |= SELERR;
                DBGPR (2, "IODevTC08::thread: no file for drive %d\n", driveno);
                goto finerror;
            }

            // if tape stopped, we can't do anything
            if (! (shm->status_a & GOBIT)) continue;

            // blocks are conceptually stored:
            //  fwdmark          revmark
            //    <n>   <data-n>   <n>       - where 00000<=n<=02701
            //  ^     ^          ^     ^     - the tape head is at any one of these positions
            //  a     b          c     d     - letter shown on tc08status.cc output
            //  0+4n  1+4n       2+4n  3+4n  - value stored in tapepos
            // tapepos = 0 : at very beginning of tape
            // tapepos = BLOCKSPERTAPE*4-1 : at very end of tape
            // the file just contains the data, as 129 16-bit words, rjzf * 1474 blocks
            // seek forward always stops at 'b' or end-of-tape
            // seek reverse always stops at 'c' or beg-of-tape
            // read/write forward always stops at 'c' or end-of-tape
            // read/write reverse always stops at 'b' or beg-of-tape
            ASSERT (drive->tapepos < BLOCKSPERTAPE*4);

            switch ((shm->status_a & 070) >> 3) {

                // MOVE (2.5.1.4 p 27)
                case 0: {

                    // step the first one with startup delay if needed
                    if (this->delayblk ()) goto finished;
                    if (this->stepskip (drive)) goto endtape;

                    // spend at most 5 seconds to rewind tape
                    uint16_t blknum   = drive->tapepos / 4;
                    uint16_t blkstogo = REVERS ? blknum : BLOCKSPERTAPE - blknum;
                    uint32_t usperblk = (blkstogo < 200) ? 25000 : 5000000 / blkstogo;

                    // skip the rest of the way
                    while (true) {
                        if (this->delayloop (usperblk)) goto finished;
                        if (this->stepskip (drive)) goto endtape;
                    }
                }

                // SEARCH (2.5.1.4 p 27)
                case 1: {
                    uint16_t idwc, idca;
                    do {
                        if (this->delayblk ()) goto finished;
                        if (this->stepskip (drive)) goto endtape;

                        idwc = memarray[IDWC];
                        idca = memarray[IDCA];
                        ASSERT (idwc <= 07777);
                        ASSERT (idca <= 07777);
                        dyndisdma (IDWC, 1,  true, shm->dmapc);
                        dyndisdma (IDCA, 1, false, shm->dmapc);
                        dyndisdma (field + idca, 1, true, shm->dmapc);
                        DBGPR (2, "IODevTC08::thread: skip idwc=%04o idca=%o.%04o\n", idwc, field >> 12, idca);

                        idwc = (idwc + 1) & 07777;                              // update word count before writing out block number
                        memarray[IDWC] = idwc;                                  // ...os8 driver has idca==IDWC
                        memarray[field|idca] = drive->tapepos / 4;              // write out mark we just hopped over
                        DBGPR (2, "IODevTC08::thread: search memarray[IDWC] = %04o ; memarray[%05o] <= %04o\n", idwc, field | idca, drive->tapepos / 4);
                    } while (CONTIN && (idwc != 0));
                    goto success;
                }

                // READ DATA (2.5.1.5 p 27)
                case 2: {
                    uint16_t idca, idwc;
                    do {
                        if (this->delayblk ()) goto finished;
                        if (this->stepxfer (drive)) goto endtape;

                        uint16_t buff[WORDSPERBLOCK];
                        int rc = pread (drive->dtfd, buff, BYTESPERBLOCK, drive->tapepos / 4 * BYTESPERBLOCK);
                        if (rc < 0) {
                            fprintf (stderr, "IODevTC08::thread: error reading tape %d file: %m\n", driveno);
                            ABORT ();
                        }
                        if (rc != BYTESPERBLOCK) {
                            fprintf (stderr, "IODevTC08::thread: only read %d of %d bytes from tape %d file\n", rc, BYTESPERBLOCK, driveno);
                            ABORT ();
                        }
                        if (shm->debug >= 3) this->dumpbuf (drive, "read", buff, WORDSPERBLOCK);

                        idca = memarray[IDCA];
                        idwc = memarray[IDWC];
                        ASSERT (idca <= 07777);
                        ASSERT (idwc <= 07777);
                        dyndisdma (IDWC, 1, true, shm->dmapc);
                        dyndisdma (IDCA, 1, true, shm->dmapc);
                        dyndisdma (field + idca, MIN (WORDSPERBLOCK, 010000 - idwc), true, shm->dmapc);
                        DBGPR (2, "IODevTC08::thread: read idwc=%04o idca=%o.%04o block=%04o\n", idwc, field >> 12, idca, drive->tapepos / 4);
                        if (REVERS) {
                            for (int i = WORDSPERBLOCK; -- i >= 0;) {
                                idca = (idca + 1) & 07777;
                                memarray[field|idca] = ocarray[buff[i]&07777];
                                idwc = (idwc + 1) & 07777;
                                if (idwc == 0) break;
                            }
                            memarray[IDCA] = idca;
                            memarray[IDWC] = idwc;
                        } else {
                            // madness: TC08 OS/8 boot block changes from data field 0 to data field 1 mid-read
                            // so pass data s-l-o-w-l-y when booting
                            if (dmareadoverwritesinstructions (field, idca, idwc)) {
                                ASSERT (this->allowskipopt);                    // this is only thing using allowskipopt
                                this->allowskipopt = false;                     // don't allow to enter skipopt wait
                                while (this->dskpwait) {                        // break out of skipopt wait if already in one
                                    setintreqmask (0);                          // wake it up
                                    pthread_mutex_unlock (&shm->lock);          // give it time to wake up
                                    usleep (1000);
                                    pthread_mutex_lock (&shm->lock);
                                }
                                for (int i = 0; i < WORDSPERBLOCK; i ++) {
                                    shm->cycles = shadow.getcycles ();          // wait for processor to run 100 cycles
                                    this->delayloop (1000);                     // ... at least 20 instructions
                                    memarray[IDWC] = idwc = (memarray[IDWC] + 1) & 07777;
                                    memarray[IDCA] = idca = (memarray[IDCA] + 1) & 07777;
                                    field = (shm->status_b & 070) << 9;
                                    DBGPR (4, "IODevTC08::thread:  slow memarray[%05o] = %04o\n", field | idca, buff[i] & 07777);
                                    memarray[field|idca] = buff[i] & 07777;     // transfer a word
                                    if (idwc == 0) break;
                                }
                                this->allowskipopt = true;
                            } else {
                                for (int i = 0; i < WORDSPERBLOCK; i ++) {
                                    idwc = (idwc + 1) & 07777;
                                    idca = (idca + 1) & 07777;
                                    DBGPR (4, "IODevTC08::thread:  rfwd memarray[%05o] = %04o\n", field | idca, buff[i] & 07777);
                                    memarray[field|idca] = buff[i] & 07777;
                                    if (idwc == 0) break;
                                }
                                memarray[IDCA] = idca;
                                memarray[IDWC] = idwc;
                            }
                        }
                    } while (CONTIN && (idwc != 0));
                    goto success;
                }

                // READ ALL
                // - runs MAINDEC D3RA test (forward and reverse)
                //   let it run at least 2 passes over tape to get some read-all-reverses
                case 3: {
                    uint16_t idca, idwc;
                    do {
                        if (this->delayblk ()) goto finished;
                        if (this->stepxfer (drive)) goto endtape;

                        // read 129 data words from file
                        // leave room for header words
                        uint16_t buff[5+WORDSPERBLOCK+5];
                        uint16_t blknum = drive->tapepos / 4;
                        uint16_t *databuff = &buff[5];
                        int rc = pread (drive->dtfd, databuff, BYTESPERBLOCK, blknum * BYTESPERBLOCK);
                        if (rc < 0) {
                            fprintf (stderr, "IODevTC08::thread: error reading tape %d file: %m\n", driveno);
                            ABORT ();
                        }
                        if (rc != BYTESPERBLOCK) {
                            fprintf (stderr, "IODevTC08::thread: only read %d of %d bytes from tape %d file\n", rc, BYTESPERBLOCK, driveno);
                            ABORT ();
                        }

                        // make up header words tacked on beginning and end of data words
                        ASSERT (blknum <= 07777);
                        if (REVERS) {
                            buff[WORDSPERBLOCK+9] = 0;
                            buff[WORDSPERBLOCK+8] = ocarray[blknum];
                            buff[WORDSPERBLOCK+7] = 0;
                            buff[WORDSPERBLOCK+6] = 0;
                            buff[WORDSPERBLOCK+5] = 07700;
                            uint16_t parity = 0;
                            for (int i = 0; i < WORDSPERBLOCK; i ++) parity ^= databuff[i] ^ (databuff[i] >> 6);
                            buff[4] = parity & 00077;
                            buff[3] = 0;
                            buff[2] = 0;
                            buff[1] = blknum;
                            buff[0] = 0;
                        } else {
                            buff[0] = 0;
                            buff[1] = blknum;
                            buff[2] = 0;
                            buff[3] = 0;
                            buff[4] = 00077;
                            uint16_t parity = 0;
                            for (int i = 0; i < WORDSPERBLOCK; i ++) parity ^= databuff[i] ^ (databuff[i] << 6);
                            buff[WORDSPERBLOCK+5] = parity & 07700;
                            buff[WORDSPERBLOCK+6] = 0;
                            buff[WORDSPERBLOCK+7] = 0;
                            buff[WORDSPERBLOCK+8] = ocarray[blknum];
                            buff[WORDSPERBLOCK+9] = 0;
                        }

                        if (shm->debug >= 3) this->dumpbuf (drive, "rall", buff, 5 + WORDSPERBLOCK + 1);

                        // copy out to dma buffer
                        idca = memarray[IDCA];
                        idwc = memarray[IDWC];
                        ASSERT (idca <= 07777);
                        ASSERT (idwc <= 07777);
                        dyndisdma (IDWC, 1, true, shm->dmapc);
                        dyndisdma (IDCA, 1, true, shm->dmapc);
                        dyndisdma (field + idca, MIN (5 + WORDSPERBLOCK + 1, 010000 - idwc), true, shm->dmapc);
                        DBGPR (2, "IODevTC08::thread: rall idwc=%04o (%4u) idca=%o.%04o block=%04o\n", idwc, (010000 - idwc), field >> 12, idca, blknum);
                        if (REVERS) {
                            for (int i = 5 + WORDSPERBLOCK + 5; -- i >= 0;) {
                                idca = (idca + 1) & 07777;
                                memarray[field|idca] = ocarray[buff[i]&07777];
                                idwc = (idwc + 1) & 07777;
                                if (idwc == 0) break;
                            }
                        } else {
                            for (int i = 0; i < 5 + WORDSPERBLOCK + 5; i ++) {
                                idwc = (idwc + 1) & 07777;
                                idca = (idca + 1) & 07777;
                                DBGPR (4, "IODevTC08::thread:  rall memarray[%05o] = %04o\n", field | idca, buff[i] & 07777);
                                memarray[field|idca] = buff[i] & 07777;
                                if (idwc == 0) break;
                            }
                        }
                        memarray[IDCA] = idca;
                        memarray[IDWC] = idwc;
                    } while (CONTIN && (idwc != 0));
                    goto success;
                }

                // WRITE DATA (2.5.1.7 p 28)
                case 4: {
                    if (shm->drives[driveno].rdonly) {
                        DBGPR (2, "IODevTC08::thread: write attempt on read-only drive %d\n", driveno);
                        shm->status_b |= SELERR;
                        goto finerror;
                    }

                    uint16_t idca, idwc;
                    do {
                        if (this->delayblk ()) goto finished;
                        if (this->stepxfer (drive)) goto endtape;

                        uint16_t buff[WORDSPERBLOCK];
                        idca = memarray[IDCA];
                        idwc = memarray[IDWC];
                        ASSERT (idca <= 07777);
                        ASSERT (idwc <= 07777);
                        dyndisdma (IDWC, 1, true, shm->dmapc);
                        dyndisdma (IDCA, 1, true, shm->dmapc);
                        dyndisdma (field + idca, MIN (WORDSPERBLOCK, 010000 - idwc), false, shm->dmapc);
                        DBGPR (2, "IODevTC08::thread: write idwc=%04o idca=%o.%04o block=%04o\n", idwc, field >> 12, idca, drive->tapepos / 4);
                        if (REVERS) {
                            for (int i = WORDSPERBLOCK; i > 0;) {
                                idca = (idca + 1) & 07777;
                                buff[--i] = ocarray[memarray[field|idca]&07777];
                                idwc = (idwc + 1) & 07777;
                                if (idwc == 0) {
                                    while (-- i >= 0) buff[i] = 07777;
                                    break;
                                }
                            }
                        } else {
                            for (int i = 0; i < WORDSPERBLOCK;) {
                                idca = (idca + 1) & 07777;
                                buff[i++] = memarray[field|idca] & 07777;
                                idwc = (idwc + 1) & 07777;
                                if (idwc == 0) {
                                    memset (&buff[i], 0, (WORDSPERBLOCK - i) * 2);
                                    break;
                                }
                            }
                        }
                        memarray[IDCA] = idca;
                        memarray[IDWC] = idwc;

                        if (shm->debug >= 3) this->dumpbuf (drive, "write", buff, WORDSPERBLOCK);
                        int rc = pwrite (drive->dtfd, buff, BYTESPERBLOCK, drive->tapepos / 4 * BYTESPERBLOCK);
                        if (rc < 0) {
                            fprintf (stderr, "IODevTC08::thread: error writing tape %d file: %m\n", driveno);
                            ABORT ();
                        }
                        if (rc != BYTESPERBLOCK) {
                            fprintf (stderr, "IODevTC08::thread: only wrote %d of %d bytes to tape %d file\n", rc, BYTESPERBLOCK, driveno);
                            ABORT ();
                        }
                    } while (CONTIN && (idwc != 0));
                    goto success;
                }

                default: {
                    fprintf (stderr, "IODevTC08::thread: unsupported command %u\n", ((shm->status_a & 00070) >> 3));
                    shm->status_b |= SELERR;
                    goto finerror;
                }
            }
            ABORT ();
        endtape:;
            DBGPR (2, "IODevTC08::thread: - end of tape\n");
            shm->status_b |=  ENDTAP;   // set up end-of-tape status
        finerror:;
            shm->status_a &= ~ GOBIT;   // any error shuts the GO bit off
            goto finished;
        success:;
            DBGPR (2, "IODevTC08::thread: - final idwc=%04o idca=%o.%04o\n", memarray[IDWC], field >> 12, memarray[IDCA]);
            shm->status_b |=  DTFLAG;   // errors do not get DTFLAG
            // if normal mode with non-zero remaining IDWC,
            //  real dectapes will start the next transfer when the next bits come under the tape head in a few milliseconds
            //    failing with timing error if DTFLAG has not been cleared by the processor by then
            //  in our case, we process the next block when the processor clears DTFLAG because the tubes may take a while to clear DTFLAG
        finished:;
            DBGPR (1, "IODevTC08::thread: st_B=%04o idwc=%04o->%04o\n", shm->status_b, oldidwc, memarray[IDWC]);

            // maybe request an interrupt
            this->updateirq ();

            // if drive is running and we don't get another command in UNLOADNS, unload it
            if (shm->status_a & GOBIT) {
                drive->unldat = getnowns () + UNLOADNS;
            } else {
                drive->unldat = 0xFFFFFFFFFFFFFFFFULL;
            }
        }
    }

    // ioreset(), unlock and exit thread
    pthread_mutex_unlock (&shm->lock);
}

// step tape just before data in the current tape direction
//  returns false: tapepos updated as described
//           true: hit end-of-tape
//                 tapepos set to whichever end we're at
bool IODevTC08::stepskip (IODevTC08Drive *drive)
{
    if (REVERS) {
        if (drive->tapepos <= 2) {
            drive->tapepos = 0;
            return true;
        }
        switch (drive->tapepos & 3) {
            case 0: drive->tapepos -= 2; break;
            case 1: drive->tapepos -= 3; break;
            case 2: drive->tapepos -= 4; break;
            case 3: drive->tapepos --;   break;
        }
    } else {
        switch (drive->tapepos & 3) {
            case 0: drive->tapepos ++;   break;
            case 1: drive->tapepos += 4; break;
            case 2: drive->tapepos += 3; break;
            case 3: drive->tapepos += 2; break;
        }
        if (drive->tapepos >= BLOCKSPERTAPE*4) {
            drive->tapepos = BLOCKSPERTAPE*4 - 1;
            return true;
        }
    }
    return false;
}

// step tape just after data in the current tape direction
//  returns false: tapepos updated as described
//           true: hit end-of-tape
//                 tapepos set to whichever end we're at
bool IODevTC08::stepxfer (IODevTC08Drive *drive)
{
    if (REVERS) {
        if (drive->tapepos <= 1) {
            drive->tapepos = 0;
            return true;
        }
        switch (drive->tapepos & 3) {
            case 0: drive->tapepos -= 3; break;
            case 1: drive->tapepos -= 4; break;
            case 2: drive->tapepos --;   break;
            case 3: drive->tapepos -= 2; break;
        }
    } else {
        switch (drive->tapepos & 3) {
            case 0: drive->tapepos += 2; break;
            case 1: drive->tapepos ++;   break;
            case 2: drive->tapepos += 4; break;
            case 3: drive->tapepos += 3; break;
        }
        if (drive->tapepos >= BLOCKSPERTAPE*4) {
            drive->tapepos = BLOCKSPERTAPE*4 - 1;
            return true;
        }
    }
    return false;
}

// dump block buffer
void IODevTC08::dumpbuf (IODevTC08Drive *drive, char const *label, uint16_t const *buff, int nwords)
{
    fprintf (stderr, "IODevTC08::dumpbuf: %o  %5s %s  block %04o\n", (int) (drive - shm->drives), label, (REVERS ? "REV" : "FWD"), drive->tapepos / 4);
    for (int i = 0; i < nwords; i += 16) {
        fprintf (stderr, "  %04o:", i);
        for (int j = 0; (j < 16) && (i + j < nwords); j ++) {
            fprintf (stderr, " %04o", buff[i+j]);
        }
        fprintf (stderr, "\n");
    }
}

// see if a dma read will overwrite instructions currently executing
//  input:
//   field = dma transfer field in <14:12>, rest is zeroes
//   idca = start of transfer - 1
//   idwc = 2's comp transfer word count
static bool dmareadoverwritesinstructions (uint16_t field, uint16_t idca, uint16_t idwc)
{
    // frame must match exactly
    uint16_t curif = memext.iframe;
    if (curif != field) return false;

    // current PC must be within transfer area
    uint16_t endaddr = (idca - idwc) & 07777;
    idca = (idca + 1) & 07777;
    uint16_t curpc = shadow.r.pc;
    if (endaddr >= idca) {
        if ((curpc < idca) || (curpc > endaddr)) return false;
    } else {
        if ((curpc < idca) && (curpc > endaddr)) return false;
    }
    return true;
}

// delay processing for a block
//  returns:
//   false = it's ok to keep going as is
//    true = something changed, re-decode
bool IODevTC08::delayblk ()
{
    // 25ms standard per-block delay
    int usec = 25000;

    // 375ms additional for startup delay
    if (shm->startdelay) {
        shm->startdelay = false;
        usec += 375000;
    }

    return this->delayloop (usec);
}

// delay the given number of microseconds, unlocking during the wait
// check for changed command during the wait
// also make sure processor has executed at least 100 cycles since i/o instruction
// ...so processor has time to set up dma descriptor words after starting the i/o
//  output:
//   returns true: command changed during wait
//          false: command remained the same
bool IODevTC08::delayloop (int usec)
{
    // detect if status_a register changed while unlocked
    uint16_t savesta = shm->status_a;

    while (true) {

        // unlock while waiting (so we don't block processor doing i/o instructions)
        pthread_mutex_unlock (&shm->lock);
        usleep (usec);
        pthread_mutex_lock (&shm->lock);

        // tell caller to abort if resetting or status_a written
        if (shm->iopend || (shm-> status_a != savesta) || shm->resetting) return true;

        // the TC08 diagnostics do the I/O instruction to start the I/O THEN write IDCA and IDWC,
        // so make sure CPU has executed at least 100 cycles (20..30 instructions) or is doing an WFI
        if (waitingforinterrupt) return false;                  // WFI is ok (processor won't cycle), assume IDCA,IDWC set up
        uint64_t ncycles = shadow.getcycles () - shm->cycles;   // see how many cycles since I/O started
        if (ncycles >= 100) return false;                       // if 100 cycles, assume IDCA,IDWC set up

        // not yet, wait another millisecond
        usec = 1000;
    }
}

// update interrupt request
// interrupt if enabled and command has completed
void IODevTC08::updateirq ()
{
    if ((shm->status_a & INTENA) && (shm->status_b & INTREQ)) {
        setintreqmask (IRQ_DTAPE);
    } else {
        clrintreqmask (IRQ_DTAPE, this->dskpwait && (shm->status_b & INTREQ));
    }
}

// unload the drive
void IODevTC08::unloadrive (int driveno)
{
    IODevTC08Drive *drive = &shm->drives[driveno];
    close (drive->dtfd);
    drive->dtfd = -1;
    drive->unldat = 0xFFFFFFFFFFFFFFFFULL;
    fprintf (stderr, "IODevTC08::unloadrive: drive %d unloaded\n", driveno);
}

// print message if debug is at or above the given level
void IODevTC08::dbgpr (int level, char const *fmt, ...)
{
    if (shm->debug >= level) {
        va_list ap;
        va_start (ap, fmt);
        vfprintf (stderr, fmt, ap);
        va_end (ap);
    }
}

// get time that pthread_cond_timedwait() is based on
static uint64_t getnowns ()
{
    struct timespec nowts;
    if (clock_gettime (CLOCK_REALTIME, &nowts) < 0) ABORT ();
    return ((uint64_t) nowts.tv_sec) * 1000000000 + nowts.tv_nsec;
}

// contents of a freshly zeroed dectape in OS/8
static uint16_t const formatofs = 0001000;
static uint16_t const formatbuf[] = {
    000000, 000000, 007777, 000007, 000000, 000000, 007777, 000000,
    006446, 000000, 003032, 001777, 003024, 005776, 001375, 003267,
    006201, 001744, 003667, 007040, 001344, 003344, 007040, 001267,
    002020, 005215, 007200, 006211, 005607, 000201, 000440, 002331,
    002324, 000515, 004010, 000501, 000400, 001774, 001373, 003774,
    001774, 000372, 001371, 003770, 001263, 003767, 003032, 001777,
    003024, 006202, 004424, 000200, 003400, 000007, 005766, 004765,
    005776, 000000, 001032, 007650, 005764, 005667, 001725, 002420,
    002524, 004005, 002222, 001722, 000000, 003344, 001763, 003267,
    003204, 007346, 003207, 001667, 007112, 007012, 007012, 000362,
    007440, 004761, 002204, 005340, 002267, 002207, 005311, 001344,
    007640, 005760, 001667, 007650, 005760, 001357, 004756, 002344,
    007240, 005310, 007240, 003204, 001667, 005315, 000000, 003020,
    001411, 003410, 002020, 005346, 005744, 000000, 000000, 000000,
    005172, 000256, 004620, 004627, 000077, 005533, 005622, 006443,
    003110, 007622, 007621, 006360, 000017, 007760, 007617, 006777,
    002600, 006023, 000000, 000000, 001777, 003024, 001776, 003025,
    003775, 003774, 003773, 001776, 003772, 005600, 000000, 007346,
    004771, 001770, 007041, 001027, 007500, 005233, 003012, 001770,
    007440, 004771, 003410, 002012, 005227, 005613, 003012, 001027,
    007440, 004771, 001011, 001012, 003011, 005613, 000000, 006201,
    001653, 006211, 001367, 007640, 005766, 005643, 003605, 000000,
    004765, 007700, 004764, 000005, 001025, 001363, 007650, 002032,
    005654, 000000, 003254, 001762, 007650, 005761, 001254, 007650,
    004760, 005666, 000000, 003200, 001357, 003030, 006211, 004765,
    007700, 005315, 006202, 004600, 000210, 001400, 000001, 005756,
    003007, 001755, 001354, 007650, 005326, 001200, 001363, 007640,
    005330, 001353, 003030, 005677, 003205, 002217, 004023, 003123,
    007700, 007700, 005342, 004764, 000002, 004764, 000000, 001352,
    003751, 005750, 000000, 002030, 002014, 003205, 000070, 007710,
    001401, 005626, 000007, 003700, 003023, 007600, 000171, 003522,
    002473, 006141, 000600, 007204, 006344, 002215, 002223, 002222,
    002352, 006065, 006023, 000000, 003034, 007240, 001200, 003224,
    001377, 003624, 001776, 000375, 007650, 005600, 001374, 004773,
    005600, 001723, 005770, 004020, 001120, 004026, 006164, 000100,
    003033, 003506, 001772, 007450, 007001, 000371, 007041, 005625,
    000000, 001770, 003246, 006202, 004646, 000011, 000000, 007667,
    006212, 005634, 000000, 007643, 000000, 000000, 000000, 000000,
    000000, 000000, 000000, 000000, 000000, 000000, 000000, 000000,
    000000, 000000, 000000, 000000, 000000, 000000, 000000, 000000,
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
};

static SCRetErr *writeformat (int fd)
{
    int rc = pwrite (fd, formatbuf, sizeof formatbuf, formatofs);
    if (rc != (int) sizeof formatbuf) {
        if (rc < 0) return new SCRetErr ("error writing format: %m\n");
        return new SCRetErr ("only wrote %d of %d-byte format\n", rc, (int) sizeof formatbuf);
    }
    return NULL;
}
