mrieker/pdp8v/driver/pipelib.cc

//    Copyright (C) Mike Rieker, Beverly, MA USA
//    www.outerworldapps.com
//
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
//    EXPECT it to FAIL when someone's HeALTh or PROpeRTy is at RISk.
//
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
//    http://www.gnu.org/licenses/gpl-2.0.html

// Tests the raspictl.cc program with the .mod modules using the simulation function of NetGen.java
// Slowest simulation that verifies module files

// Calling PipeLib::writegpio() cause 'force' commands to be written to NetGen
// These are read by the simulation function of NetGen.java to set the internal state of the pins.

// Reads of the GPIO pins cause 'examine' commands to be sent to NetGen.
// The simulation function of NetGen.java replies with the corresponding internal state of the pins.

// The module definitions loaded into NetGen.java must contain:
//   module proc ( various pins that would get connected to the raspberry pi )

// ./autoboardtest -pipelib -page -verbose all
// ./raspictl -printstate -randmem -pipelib

#include <errno.h>
#include <signal.h>
#include <stdio.h>
#include <stdlib.h>
#include <string.h>
#include <unistd.h>

#include "gpiolib.h"
#include "makepipelibmod.h"
#include "pindefs.h"

PipeLib::PipeLib (char const *modname)
{
    libname = "pipelib";

    // make sure modname exists in ../modules/whole.mod so netgen will find it
    // also changes "rpi" to "rpi_testpads" so gpio pins will be found
    modname = makepipelibmod (modname);

    this->modname = modname;
    this->netgenpid = 0;
    this->sendseq = 0;
}

// open connections to the java program
void PipeLib::open ()
{
    char exedir[256], netgen[256+22], modfile[256+22];

    getexedir (exedir, sizeof exedir);

    char const *netgenenv = getenv ("pipelib_netgen");
    if (netgenenv == NULL) {
        strcpy (netgen, exedir);
        strcat (netgen, "../netgen/netgen.sh");
    } else {
        strncpy (netgen, netgenenv, sizeof netgen);
        netgen[sizeof netgen-1] = 0;
    }

    char const *modfileenv = getenv ("pipelib_modfile");
    if (modfileenv == NULL) {
        strcpy (modfile, exedir);
        strcat (modfile, "../modules/whole.mod");
    } else {
        strncpy (modfile, modfileenv, sizeof modfile);
        modfile[sizeof modfile-1] = 0;
    }

    fprintf (stderr, "PipeLib::open: netgen=%s\n", netgen);
    fprintf (stderr, "PipeLib::open: modfile=%s\n", modfile);

    // fork subprocess that runs simulator
    int frnetgenfds[2] = { -1, -1 };
    int tonetgenfds[2] = { -1, -1 };

    if (pipe (frnetgenfds) < 0) ABORT ();
    if (pipe (tonetgenfds) < 0) ABORT ();
    int subpid = fork ();
    if (subpid < 0) ABORT ();
    if (subpid == 0) {
        if (dup2 (tonetgenfds[0], 0) < 0) ABORT ();
        if (dup2 (frnetgenfds[1], 1) < 0) ABORT ();
        ::close (tonetgenfds[0]);
        ::close (tonetgenfds[1]);
        ::close (frnetgenfds[0]);
        ::close (frnetgenfds[1]);
        if (setpgid (0, 0) < 0) ABORT ();
        execl (netgen, netgen, modfile, "-sim", "-", NULL);
        fprintf (stderr, "PipeLib::open: error execing %s: %m\n", netgen);
        ABORT ();
    }
    netgenpid = subpid;
    ::close (tonetgenfds[0]);
    ::close (frnetgenfds[1]);

    // write simulator TCL commands to this pipe
    sendfile = fdopen (tonetgenfds[1], "w");
    if (sendfile == NULL) ABORT ();

    setlinebuf (sendfile);

    // read simulator output from this pipe
    recvfile = fdopen (frnetgenfds[0], "r");
    if (recvfile == NULL) ABORT ();

    // step sim this many times between clock transitions
    runcount = getenv ("pipelib_runcount");
    if (runcount == NULL) runcount = "150";
    fprintf (stderr, "PipeLib::open: runcount=%s\n", runcount);

    // tell simulator what module to simulate
    // ...it has the gpio and 32-pin connectors as inputs/outputs
    fprintf (stderr, "PipeLib::open: modname=%s\n", modname);
    fprintf (sendfile, "module %s\n", modname);
    //fprintf (sendfile, "monitor fetch1q/seq fetch2q/seq defer1q/seq defer2q/seq defer3q/seq exec1q/seq exec2q/seq exec3q/seq intak1q/seq irq/seq\n");
    //fprintf (sendfile, "monitor irq/seq acq _aluq maq _alua/alu _alub/alu\n");
}

void PipeLib::close ()
{
    if (netgenpid > 0) {
        kill (netgenpid, SIGKILL);
        netgenpid = 0;
    }
    if (sendfile != NULL) {
        fclose (sendfile);
        sendfile = NULL;
    }
    if (recvfile != NULL) {
        fclose (recvfile);
        recvfile = NULL;
    }
}

// delay half a clock cycle
void PipeLib::halfcycle (bool aluadd, bool topoloop)
{
    // tell sim how much to run
    fprintf (sendfile, "run %s\n", runcount);

    // force simulation to run before we return
    // - dumps any monitor command output before returning
    ////????////examine ("[examine _JUMP]");  //// undefined for module "seq", ie, when just using paddles
}
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
